tadfmac/Canzasi/boards/SimpleShield/v0.2/eagle/SimpleShield.sch

## EAGLE design boards/SimpleShield/v0.2/eagle/SimpleShield.sch (2017-03-23)

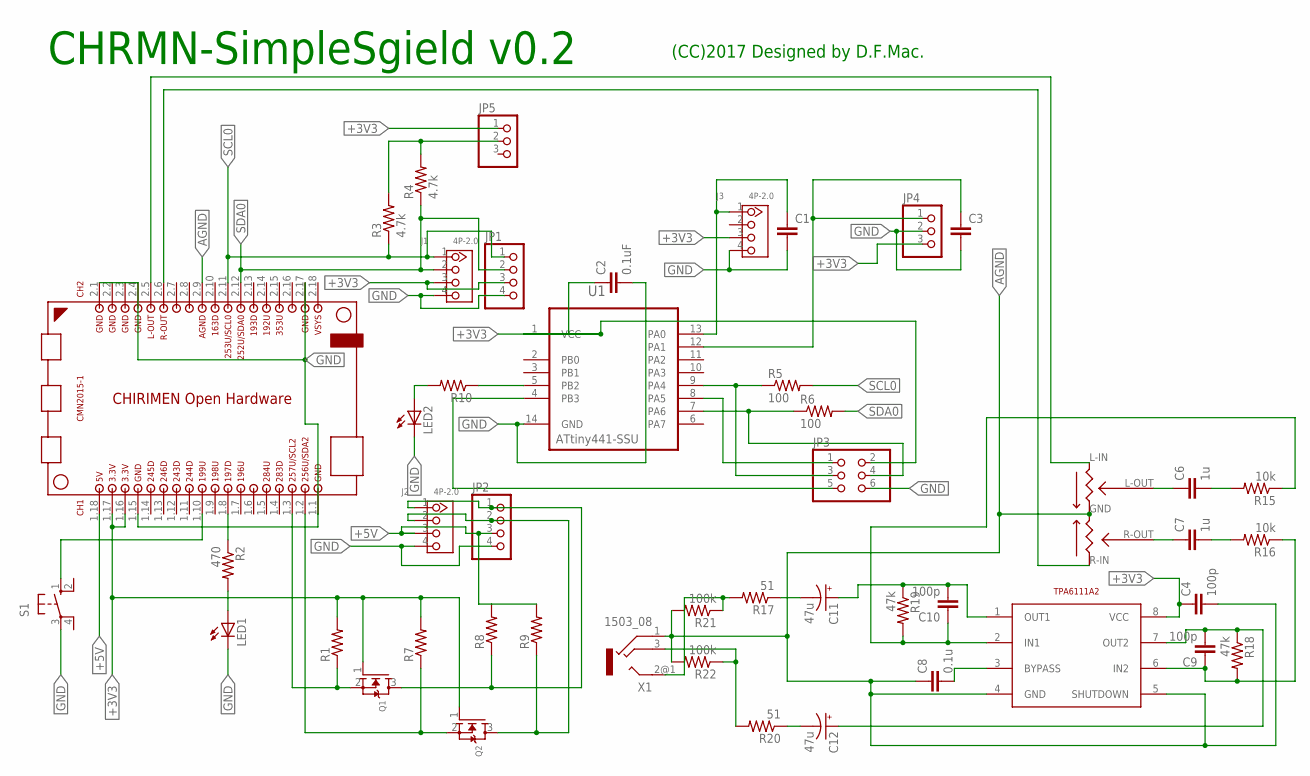
[picture p18: schematic SimpleShield.sch]

Parts:
C1, C3: C-EUC0805; C0805
C2: 0.1uF; C0805
C4, C9, C10: 100p; C0603K
C6, C7: 1u; C0603K
C8: 0.1u; C0603K
C11, C12: 47u; 153CLV-0605
J1, J2, J3: 4P-2.0; HW4-2.0
JP1, JP2: PINHD-1X4; 1X04
JP3: PINHD-2X3; 2X03
JP4, JP5: PINHD-1X3; 1X03
LED1, LED2: LED3MM
Q1, Q2: MOSFET-NREFLOW; SOT23
R1, R7, R8, R9, R10: R-US_R0603; R0603
R2: 470; R0603
R3, R4: 4.7k; R0603
R5, R6: 100; R0603
R15, R16: 10k; R0603
R17, R20: 51; R0603
R18, R19: 47k; R0603
R21, R22: 100k; R0603
S1: 10-XX; B3F-10XX
U1: ATTINY44A-SSU; SOIC127P600X175-14N
U$1: CMN2015-1SMALL; CHMN2015-1-SMALL
U$4: 5PIN-RADIO-POT
U$5: TPA6111A2; MSOP8
X1: 1503_08

Connections:
+3V3: C2.1, C4.1, J1.3, J3.3, JP1.3, JP3.2, JP4.3, JP5.1, Q1.1 (G), Q2.1 (G), R1.2, R7.2, U1.1 (VCC), U$1.1.16 (CH1-16), U$1.1.17 (CH1-17), U$5.8 (VCC)
+5V: J2.3, JP2.3, R8.2, R9.2, U$1.1.18 (CH1-18)
AGND: C4.2, C8.1, R21.2, R22.2, U$1.2.9 (CH2-9), U$4.GND, U$5.4 (GND), U$5.5 (SHUTDOWN), X1.1 (GND)
GND: C1.2, C2.2, C3.2, J1.4, J2.4, J3.4, JP1.4, JP2.4, JP3.6, JP4.2, LED1.K (C), LED2.K (C), S1.3, U1.14 (GND), U$1.1.1 (CH1-1), U$1.1.15 (CH1-15), U$1.2.1 (CH2-1), U$1.2.2 (CH2-2), U$1.2.3 (CH2-3), U$1.2.4 (CH2-4), U$1.2.17 (CH2-17)
unnamed: LED1.A, R2.2
unnamed: R2.1, U$1.1.8 (CH1-8)
unnamed: S1.1 (S), U$1.1.10 (CH1-10)
unnamed: JP3.1, U1.8 (PA5)
unnamed: JP3.3, R5.1, U1.9 (PA4)
unnamed: JP3.5, U1.4 (PB3)
unnamed: JP3.4, R6.1, U1.7 (PA6)
unnamed: C1.1, J3.1, U1.13 (PA0)
unnamed: J2.1, JP2.1, Q1.3 (D), R8.1
unnamed: J2.2, JP2.2, Q2.3 (D), R9.1
unnamed: C3.1, JP4.1, U1.12 (PA1)
unnamed: R10.1, U1.5 (PB2)
unnamed: LED2.A, R10.2
unnamed: JP5.2, R3.2, R4.2
unnamed: R17.2, R21.1, X1.2@1 (L)
unnamed: U$1.2.5 (CH2-5), U$4.L-IN (IN-L)
unnamed: U$1.2.6 (CH2-6), U$4.R-IN (IN-R)
unnamed: C6.1, U$4.L-OUT (OUT-L)
unnamed: C7.1, U$4.R-OUT (OUT-R)
unnamed: C6.2, R15.2
unnamed: C7.2, R16.2
unnamed: C10.1, R15.1, R19.2, U$5.2 (IN1)
unnamed: C9.1, R16.1, R18.2, U$5.6 (IN2)
unnamed: C11.-, R17.1
unnamed: C8.2, U$5.3 (BYPASS)
unnamed: C9.2, C12.+, R18.1, U$5.7 (OUT2)
unnamed: C10.2, C11.+, R19.1, U$5.1 (OUT1)
unnamed: R20.2, R22.1, X1.3 (R)
unnamed: C12.-, R20.1
SCL0: J1.1, JP1.1, R3.1, R5.2, U$1.2.11 (CH2-11)
SCL2: Q1.2 (S), R1.1, U$1.1.3 (CH1-3)
SDA0: J1.2, JP1.2, R4.1, R6.2, U$1.2.12 (CH2-12)
SDA2: Q2.2 (S), R7.1, U$1.1.2 (CH1-2)

Notes on the sheet:
ATtiny441-SSU
CHRMN-SimpleSgield v0.2
(CC)2017 Designed by D.F.Mac.
